mstraciak/flashforge-ad5m-mods/3d chameleon/STL/4tubes - guider.stl

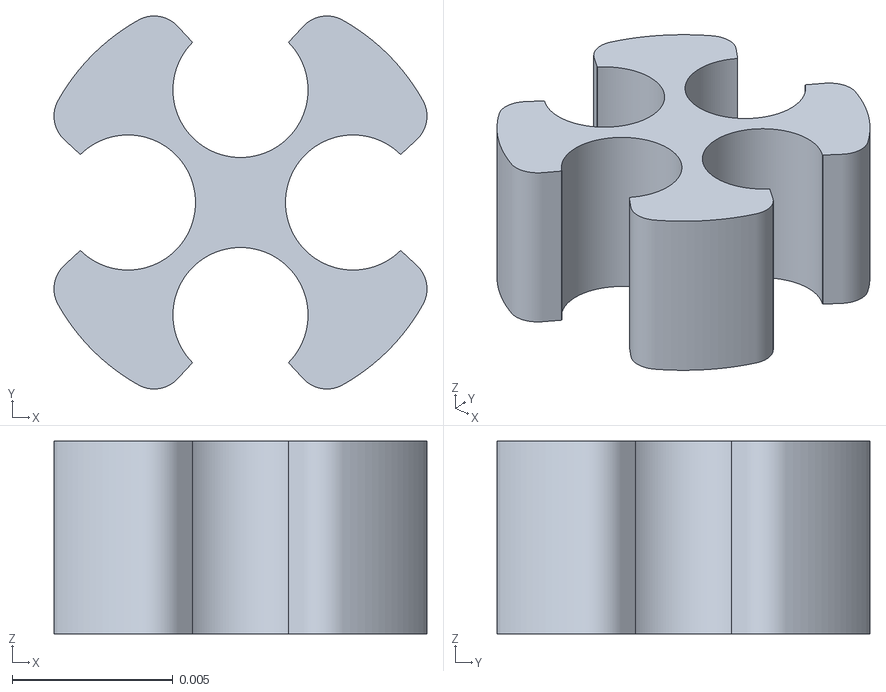
[picture p16: CAD file, 2025-04-01]
3d chameleon/STL/4tubes - guider.stl
0.0116 x 0.0116 x 0.006
