mstraciak/flashforge-ad5m-mods/HTLF with 3D Chameleon board/STLs/board_mount - chameleon.stl

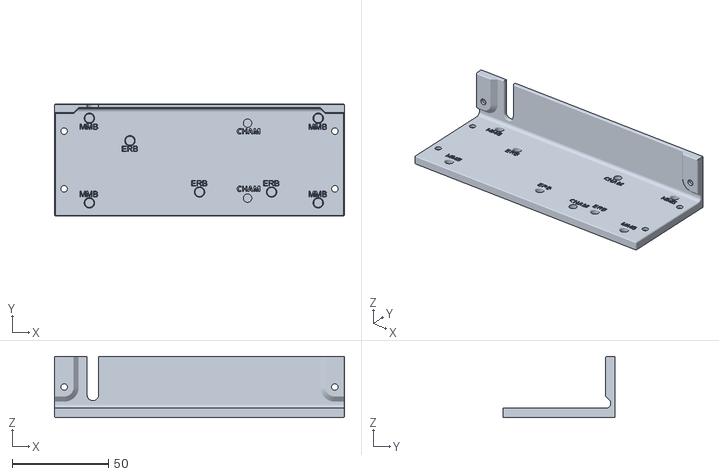
[picture p17: CAD file, 2025-12-19]
HTLF with 3D Chameleon board/STLs/board_mount - chameleon.stl
150.8 x 58.5 x 31.8
