mstraciak/flashforge-ad5m-mods/3d chameleon/manual cutter/STL/ad5m cut - block.stl

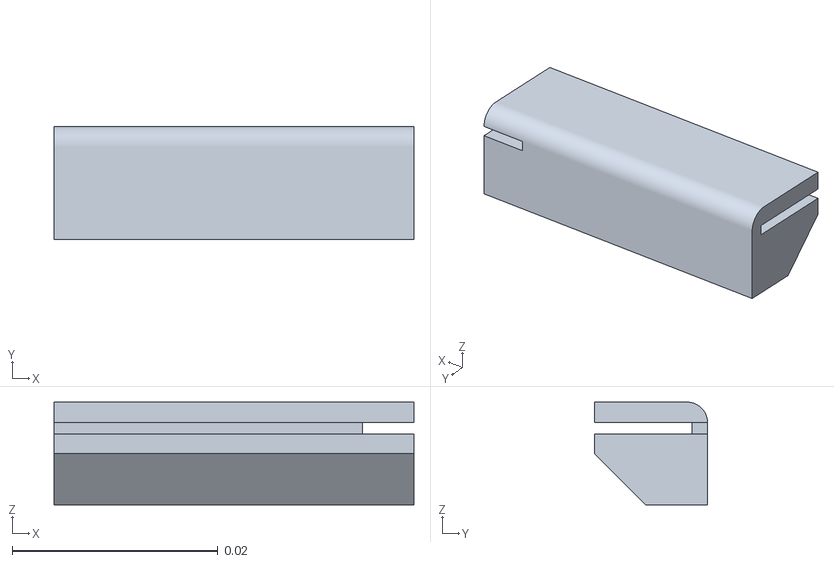
[picture p18: CAD file, 2025-04-01]
3d chameleon/manual cutter/STL/ad5m cut - block.stl
0.035 x 0.011 x 0.01
