mstraciak/flashforge-ad5m-mods/3d chameleon/manual cutter/STL/ad5m cut - arm -short.stl

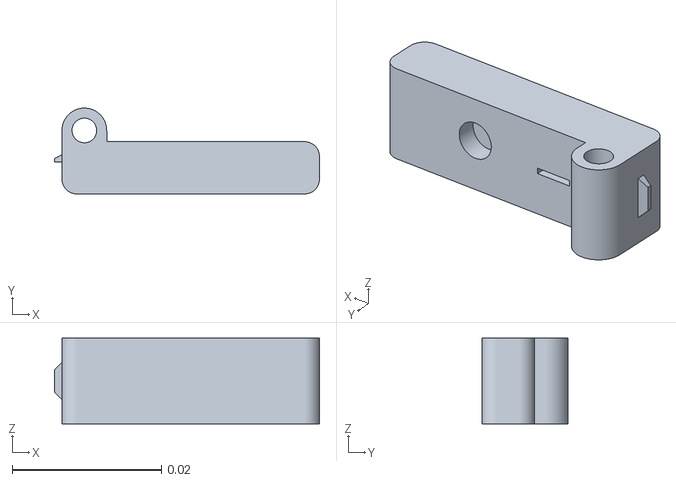
[picture p19: CAD file, 2025-04-01]
3d chameleon/manual cutter/STL/ad5m cut - arm -short.stl
0.0355 x 0.0115 x 0.0115
