mstraciak/flashforge-ad5m-mods/3d chameleon/STL/chameleon-krytkaoled13.stl

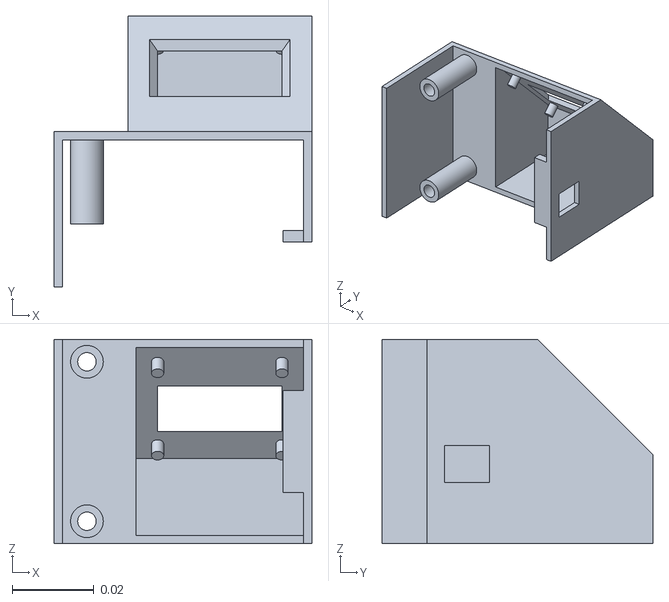
[picture p20: CAD file, 2025-03-05]
3d chameleon/STL/chameleon-krytkaoled13.stl
0.063 x 0.0663 x 0.05
