mstraciak/flashforge-ad5m-mods/3d chameleon/manual cutter/STL/ad5m cut - arm - middle.stl

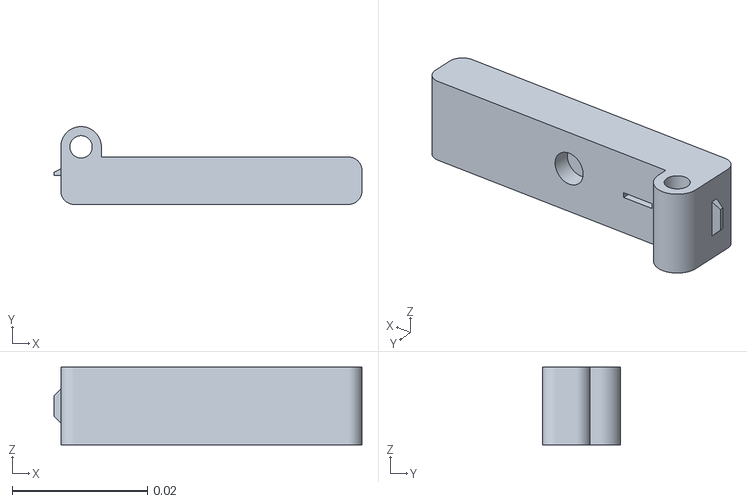
[picture p21: CAD file, 2025-04-01]
3d chameleon/manual cutter/STL/ad5m cut - arm - middle.stl
0.0455 x 0.0115 x 0.0115
