mstraciak/flashforge-ad5m-mods/3d chameleon/STL/chameleon-krytka.stl

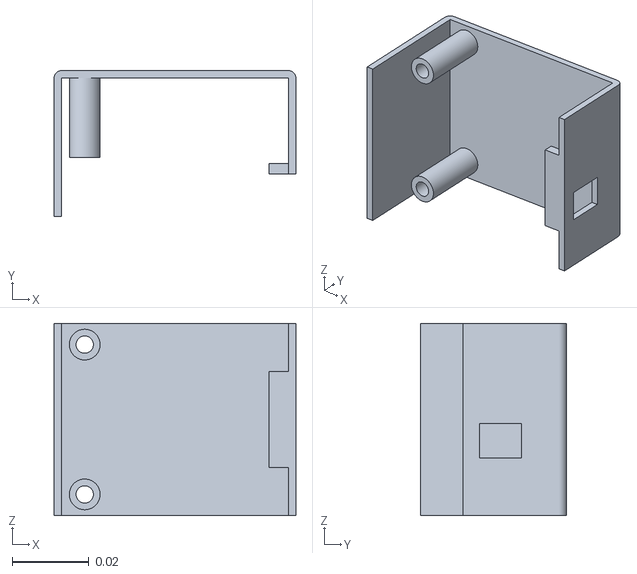
[picture p22: CAD file, 2025-03-05]
3d chameleon/STL/chameleon-krytka.stl
0.063 x 0.038 x 0.05
