mstraciak/flashforge-ad5m-mods/3d chameleon/manual cutter/STL/ad5m cut - arm - long.stl

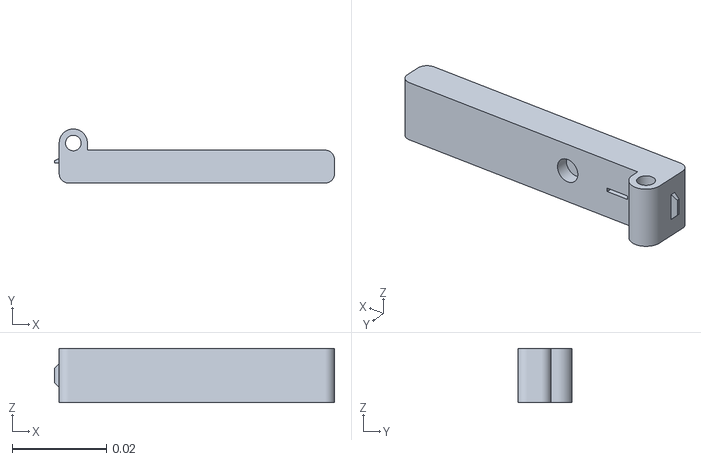
[picture p23: CAD file, 2025-04-01]
3d chameleon/manual cutter/STL/ad5m cut - arm - long.stl
0.0595 x 0.0115 x 0.0115
