mstraciak/flashforge-ad5m-mods/3d chameleon/manual cutter/img/IMG20250402203653.jpg

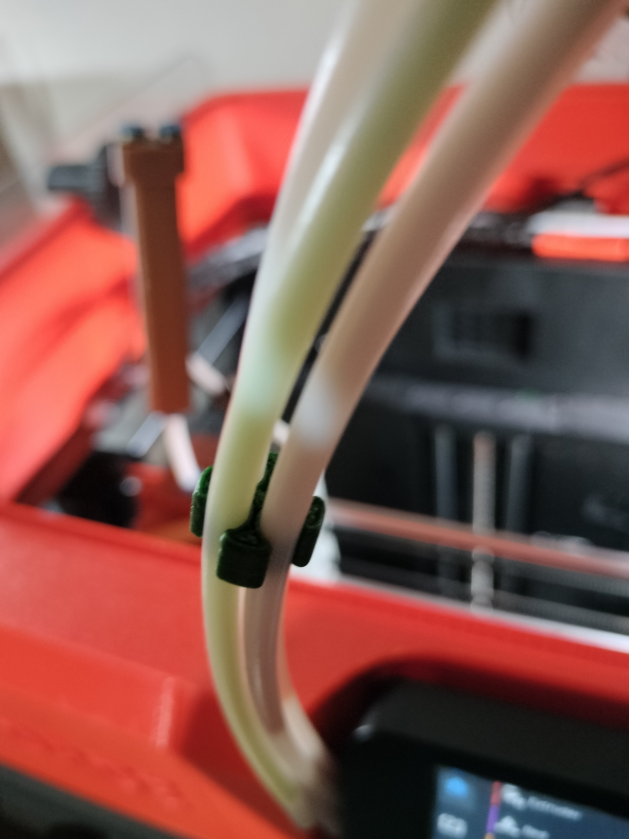
3d chameleon/manual cutter/img/IMG20250402203653.jpg
