mstraciak/flashforge-ad5m-mods/change origin of buildplate/img/orca_origin2.png

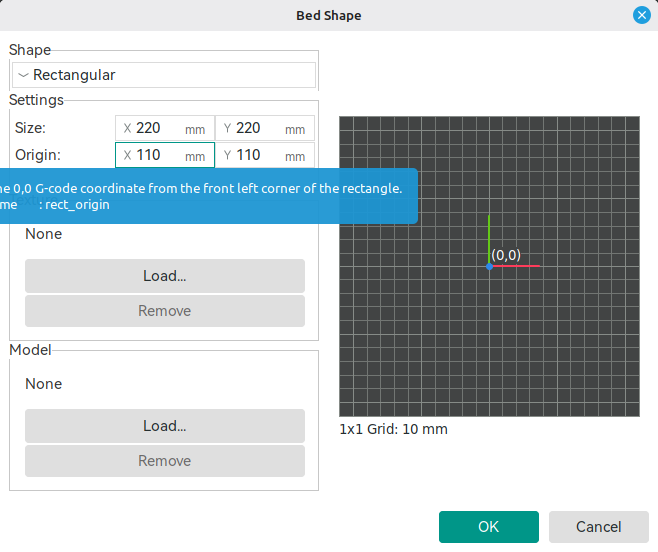
change origin of buildplate/img/orca_origin2.png
